7Upers/Aeronik09_RC/data/ir_transmitter_bb.png

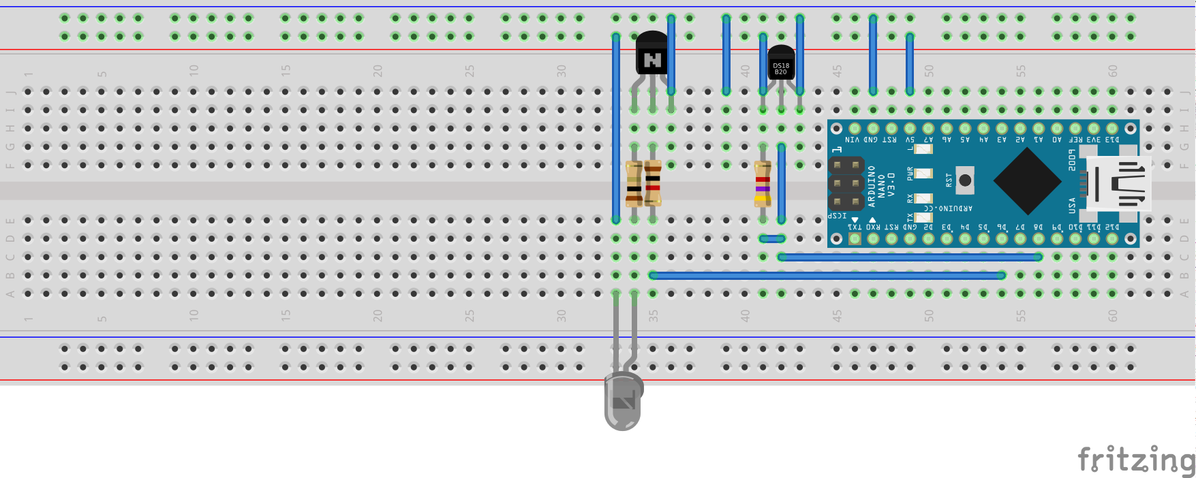
data/ir_transmitter_bb.png
