7Upers/Aeronik09_RC/data/ir_transmitter_схема.png

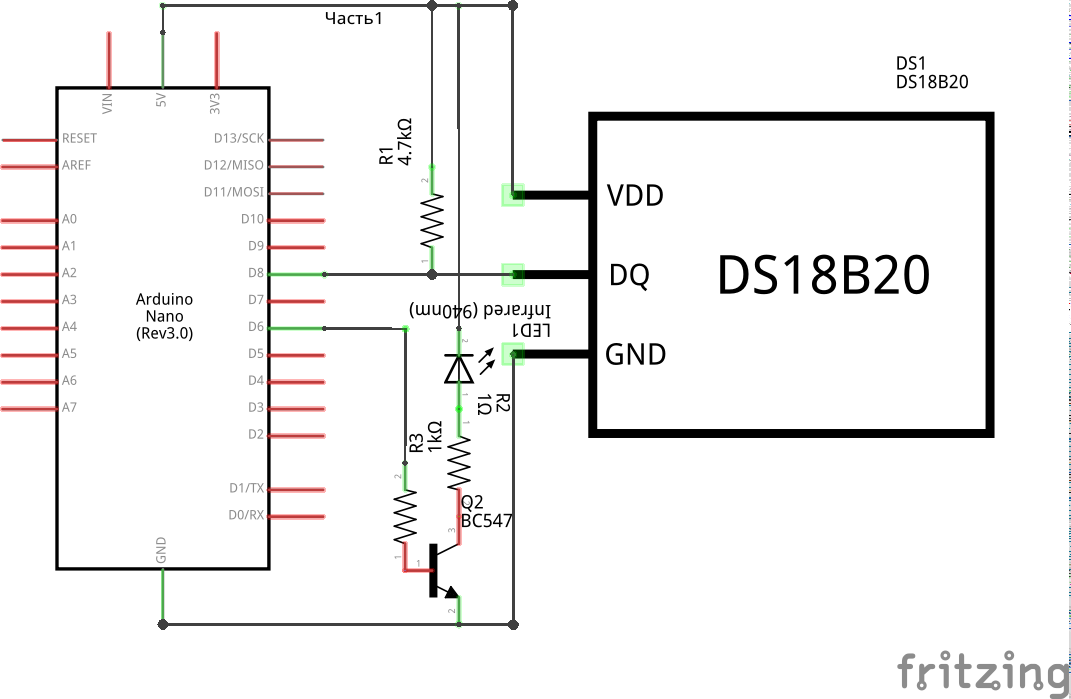
data/ir_transmitter_схема.png
